ezcGman/lora-washing-machine-sensor/pictures/install-pics/IMG_20220930_201250.jpg

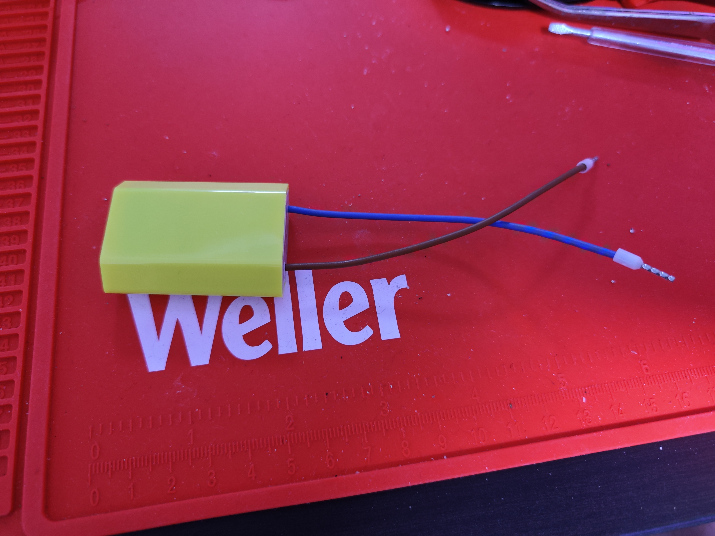
pictures/install-pics/IMG_20220930_201250.jpg
