ezcGman/lora-washing-machine-sensor/pictures/install-pics/IMG_20221001_214356.jpg

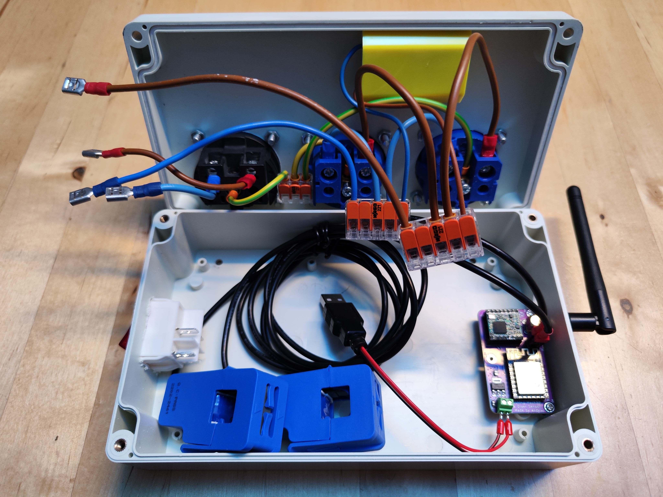
pictures/install-pics/IMG_20221001_214356.jpg
