ezcGman/lora-washing-machine-sensor/pictures/install-pics/IMG_20221001_214409.jpg

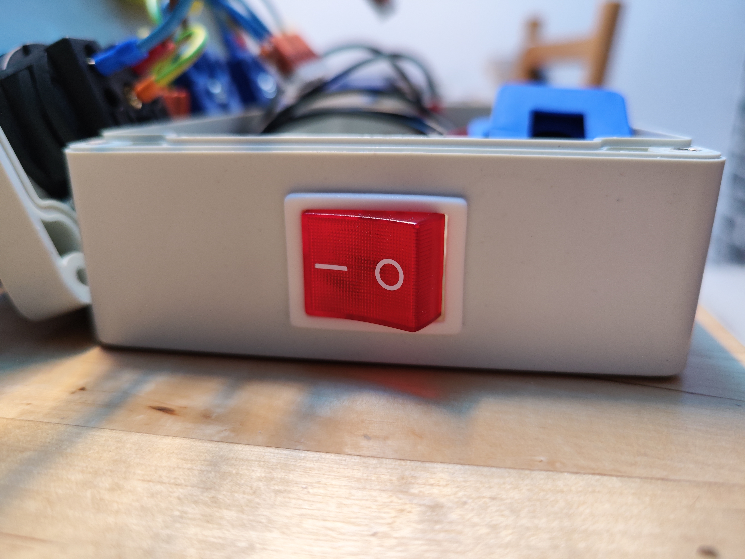
pictures/install-pics/IMG_20221001_214409.jpg
