ezcGman/lora-washing-machine-sensor/pictures/install-pics/IMG_20221001_221012.jpg

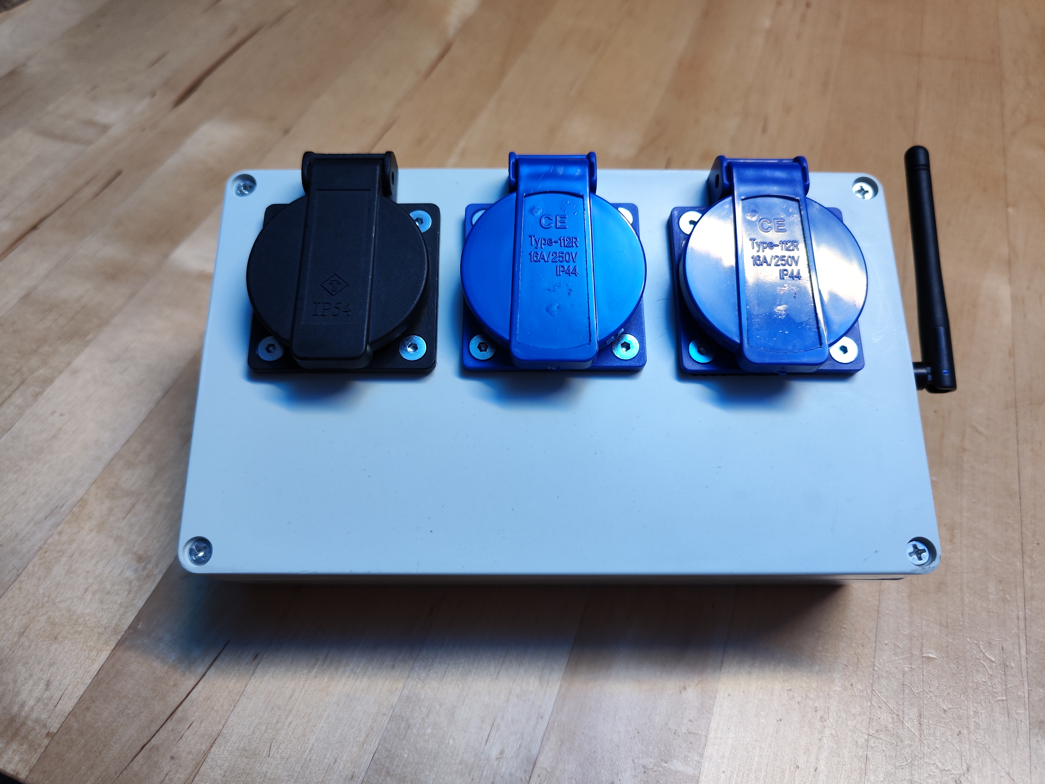
pictures/install-pics/IMG_20221001_221012.jpg
