ezcGman/lora-washing-machine-sensor/src/lora-washing-machine-sensor/lora-config.h

/* The sync word functions like a "tag": This device will onl listen to
 * messages with this sync word (tag) and completely ignore all others */
#define LORA_SYNC_WORD 0x42 // 66

/* The gateway we want to send messages to.
   If we are the gateway, make this the same as LORA_DEVICE_ID */
#define LORA_GATEWAY_ID 0x1 // 1

/* If desired change this devices ID.
 * If so, also change the LORA_DEVICE_IDS map in "lora-ids.h" */
#define LORA_DEVICE_ID 0xB // 11
#define LORA_DEVICE_ID_B 0xC // 12

#include "lora-ids.h"
